adamcritchley/all-lure/images/pcie_sata_100R.png

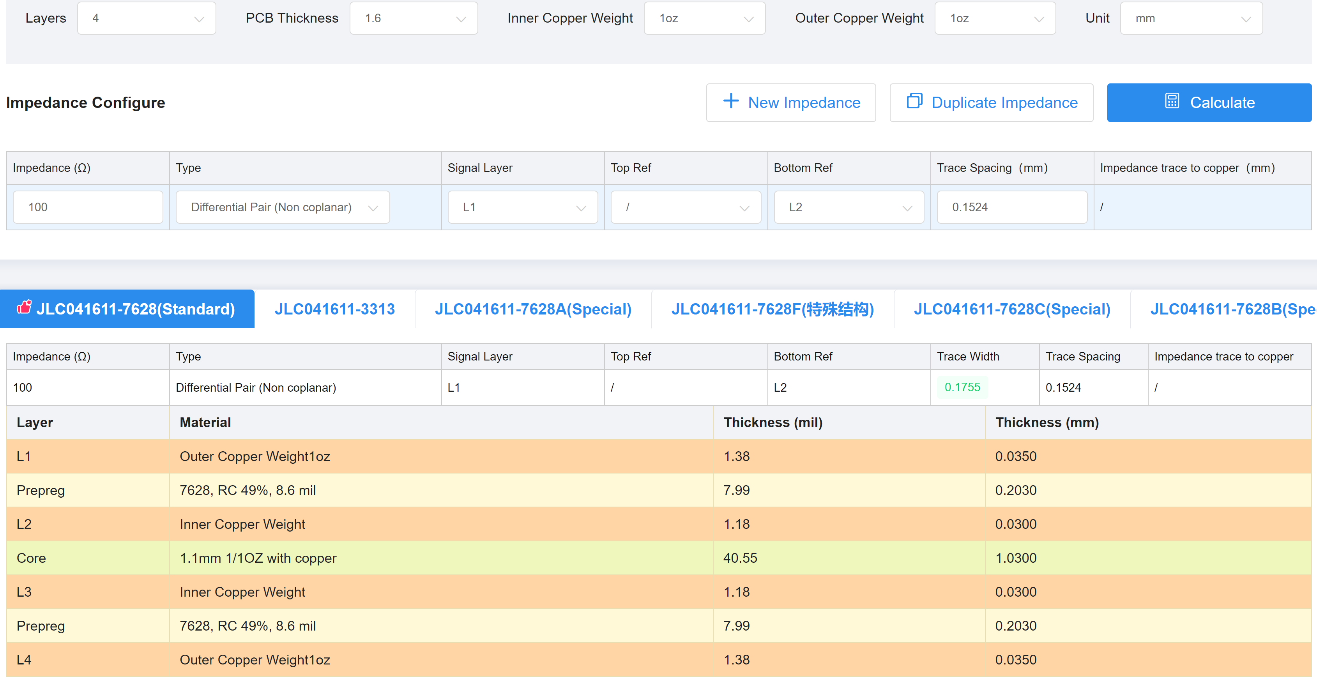
images/pcie_sata_100R.png
