adamcritchley/all-lure/images/top_with_ssd.jpg

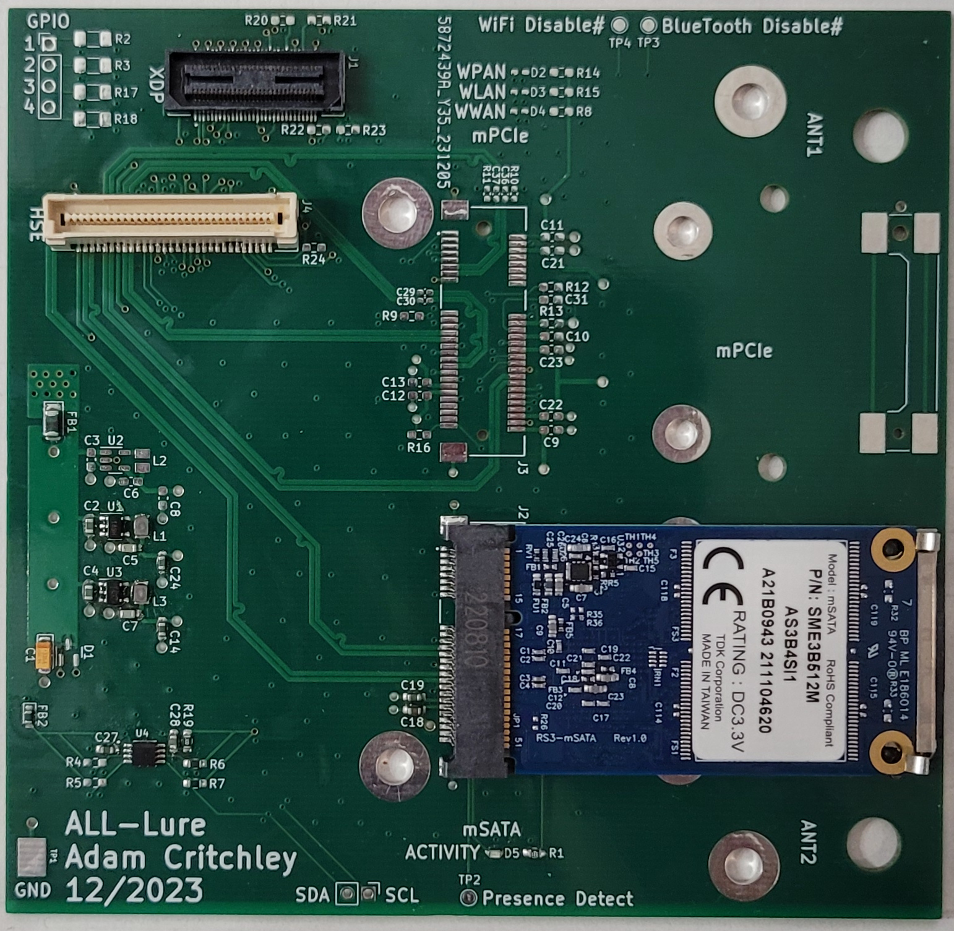
images/top_with_ssd.jpg
